RadarML/red-rover/collect/parts/src/nuc-plate.SLDPRT

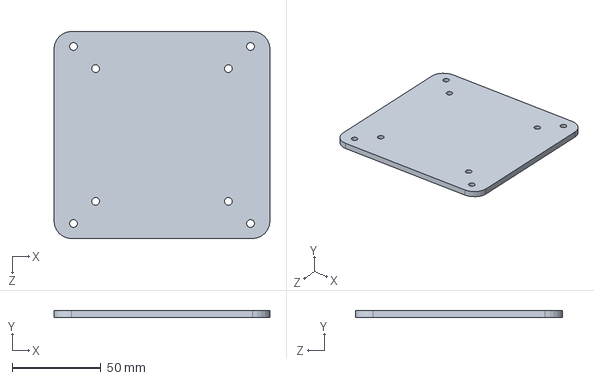
[picture p19: CAD file, 2024-02-14]
collect/parts/src/nuc-plate.SLDPRT
122.0 x 4.00 x 117.0 mm
