RadarML/red-rover/collect/roverc/lidar.py

"""Lidar data collection."""

import logging
import os
import subprocess
from queue import Queue

import numpy as np
from beartype.typing import Optional, cast
from ouster.sdk import client
from roverd import channels

from .common import Capture, Sensor, SensorException


class LidarCapture(Capture):
    """Lidar capture data."""

    def __init__(
        self, path: str, shape: tuple[int, int] = (64, 2048),
        compression: int = 0, batch: int = 12, fps: float = 1.0,
        report_interval: float = 5.0, log: Optional[logging.Logger] = None
    ) -> None:
        super().__init__(
            path=path, fps=fps, report_interval=report_interval, log=log)

        self.outputs: dict[str, Queue] = {
            channel: Queue() for channel in ["rfl", "nir", "rng"]}

        kwargs = {"preset": compression, "batch": batch}
        cast(channels.LzmaFrameChannel, self.sensor.create("rfl", {
            "format": "lzmaf", "type": "u1", "shape": shape,
            "desc": "Object NIR reflectivity"}
        )).consume(self.outputs["rfl"], thread=True, **kwargs)
        cast(channels.LzmaFrameChannel, self.sensor.create("nir", {
            "format": "lzmaf", "type": "u2", "shape": shape,
            "desc": "Near infrared ambient photons"}
        )).consume(self.outputs["nir"], thread=True, **kwargs)
        cast(channels.LzmaFrameChannel, self.sensor.create("rng", {
            "format": "lzmaf", "type": "u2", "shape": shape,
            "desc": "Range, in millimeters"}
        )).consume(self.outputs["rng"], thread=True, **kwargs)

    def queue_length(self) -> int:
        return max(v.qsize() for v in self.outputs.values())

    def write(self, data: dict[str, np.ndarray]) -> None:
        """Write compressed lzma streams."""
        for k, v in data.items():
            self.outputs[k].put(v)

    def close(self) -> None:
        """Close files and clean up."""
        for v in self.outputs.values():
            v.put(None)
        super().close()


class Lidar(Sensor):
    """Ouster Lidar sensor.

    Args:
        addr: lidar IP address; found automatically via
            `avahi-browse -lrt _roger._tcp` if not manually specified.
        port_lidar: lidar port; default 7502.
        port_imu: integrated imu port; default 7503.
        mode: lidar mode `{columns}x{fps}`.
        beams: number of lidar beams.
        name: sensor name, i.e. "lidar".
    """

    def __init__(
        self, addr: Optional[str] = None, port_lidar: int = 7502,
        port_imu: int = 7503, mode: str = "2048x10", beams: int = 64,
        name: str = "lidar"
    ) -> None:
        super().__init__(name=name)

        addr = self.get_ip() if addr is None else addr
        if addr is None:
            self.log.critical("No Ouster lidar found; is it connected?")
            raise SensorException
        self.addr = addr

        config = client.SensorConfig()  # type: ignore
        config.udp_port_lidar = port_lidar
        config.udp_port_imu = port_imu
        config.operating_mode = client.OperatingMode.OPERATING_NORMAL  # type: ignore
        config.lidar_mode = client.LidarMode.from_string(mode)  # type: ignore

        # Ouster removed the ability to calculate the resolution from the
        # mode string. Not sure why, makes absolutely no sense.
        self.fps = float(mode.split('x')[1])
        self.shape = (beams, int(mode.split('x')[0]))

        client.set_config(  # type: ignore
            self.addr, config, persist=True, udp_dest_auto=True)

        self.log.info("Initialized lidar {}: {}-beam x {} x {} fps".format(
            self.addr, *self.shape, self.fps))

    @staticmethod
    def get_ip() -> Optional[str]:
        """Get IP address of ouster sensor."""
        avahi = subprocess.run(
            ["avahi-browse", "-lrpt", "_roger._tcp"], capture_output=True)
        for service in avahi.stdout.decode('utf-8').split('\n'):
            entries = service.split(';')
            match = (
                entries[0] == '=' and
                entries[2] == 'IPv4' and
                "Ouster" in entries[3] and
                len(entries) > 8)
            if match:
                return entries[7]
        else:
            return None

    def capture(self, path: str) -> None:
        """Create capture (while `active` is set)."""
        out = LidarCapture(
            os.path.join(path, self.name), log=self.log,
            fps=self.fps, shape=self.shape, compression=0)

        stream = client.Scans.stream(  # type: ignore
            hostname=self.addr, lidar_port=7502, complete=True, timeout=1.0)
        with open(os.path.join(path, self.name, "lidar.json"), 'w') as f:
            f.write(stream.metadata.to_json_string())  # type: ignore

        for scan in stream:
            out.start()
            data = {
                "rfl": scan.field(
                    client.ChanField.REFLECTIVITY).astype(np.uint8),  # type: ignore
                "nir": scan.field(
                    client.ChanField.NEAR_IR).astype(np.uint16),  # type: ignore
                "rng": np.minimum(
                    65535, scan.field(client.ChanField.RANGE)  # type: ignore
                ).astype(np.uint16)
            }
            out.write(data)  # type: ignore
            out.end()

            if not self.active:
                break

        out.close()
